moskyt/sargans/sargans-arduino/destinations.h

const char destinations[48][47] = {
  "EC 193 | Memmingen, Muenchen Hbf",                    //    1   v1/1
  "IR 35 | Zuerich HB, Bern",                            //    2   v2/1
  "RE 54 | Versam-Safien, Ilanz",                       //    3   v1/2
  "IR 54 | Arosa",                                      //    4   v2/2
  "IC 3 | Basel",                                       //    5   v1/3
  "RJX | Wien Hbf",                                     //    6   v2/3
  "IR 54 | Einsiedeln",                                 //    7   v1/4
  "RE 51 | Netstal, Linthal",                           //    8   v2/4
  "IC 53 | Spiez, Brig",                                //    9   v1/5
  "NJ | Wien Hbf / Budapest / Prag",                    //    10  v2/5
  "RE 55 | Uznach, Nesslau",                            //    11  v1/6
  "IR 51 | Filisur, St. Moritz",                        //    12  v2/6
  "IR 53 | Romanshorn",                                 //    13  v1/7
  "IR 52 | Rheineck",                                   //    14  v2/7
  "IR 13 | Chur",                                       //    15  v1/8
  "S4 | Salez-Sennwald, St. Gallen",                    //    16  v2/8
  "TGV 9266 | Mulhouse, Paris Gare de Lyon",            //    17  v1/9
  "RE 52 | Klosters, Davos",                            //    18  v2/9
  "RE 53 | Chur, Thusis",                               //    19  v1/10
  "IC 54 | Lugano",                                     //    20  v2/10
  "ICE | Chur",                                         //    21  v1/11
  "IC 57 | Bern, Lausanne",                             //    22  v2/11
  "IC 51 | Konstanz",                                   //    23  v1/12
  "RE | Heerbrugg, St. Gallen",                         //    24  v2/12
  "RE 55 | Lavin, Scuol-Tarasp",                        //    25  v1/13
  "RJX | Zuerich HB",                                   //    26  v2/13
  "S12 | Landquart, Chur",                              //    27  v1/14
  "ICE | Basel Bad Bahnhof, Hamburg-Altona",            //    28  v2/14
  "S4 | Rorschach, Wattwil",                            //    29  v1/15
  "IR 35 | Chur",                                       //    30  v2/15
  "RE 53 | Alstaetten, Appenzell",                      //    31  v1/16
  "RE 51 | Klosters, Susch",                            //    32  v2/16
  "S4 | Walenstadt, Uznach",                            //    33  v2/17 !!
  "IC 3 | Chur",                                        //    34  v1/17 !!
  "TGV 9580 | Belfort-Montbeliard, Lyon Part Dieu",     //    35  v1/18
  "IR 51 | Wintherthur, Schaffhausen",                  //    36  v2/18
  "IR 53 | Andermatt",                                  //    37  v1/19
  "IR 55 | Zernez, Tirano",                             //    38  v2/19 
  "RE 54 | St. Margarethen",                            //    39  v2/20 !!
  "IR 13 | Heerbrugg, St. Gallen",                      //    40  v1/20 !!
  "IC 52 | Winterthur",                                 //    41  v1/21
  "IR 52 | Tarasp",                                     //    42  v1/22 !!
  "IR 55 | Appenzell",                                  //    43  v2/21 !!
  "S4 | Rorschach, Herisau",                            //    44  v2/22
  "RE 52 | Siebnen-Wangen, Pfaeffikon",                 //    45  v1/23
  "RJX | Salzburg Hbf",                                 //    46  v2/23
  "IC 55 | Oerlikon, Aarau",                            //    47  v1/24
  "IC 56 | Koblenz, Basel"                              //    48  v2/24
};
